rish987/trackswitch-manuform/things/usb_holder_cutout.stl

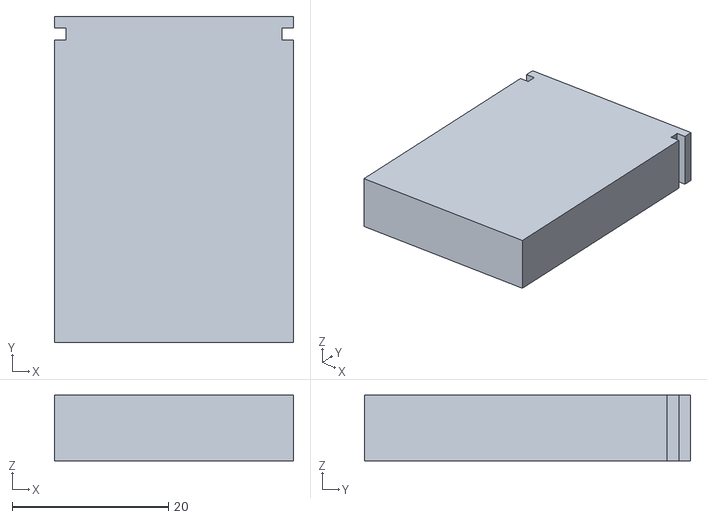
[picture p69: CAD file, 2021-12-29]
things/usb_holder_cutout.stl
30.6 x 41.7 x 8.40
