rish987/trackswitch-manuform/things/caps/matty3-deep-R5.stl

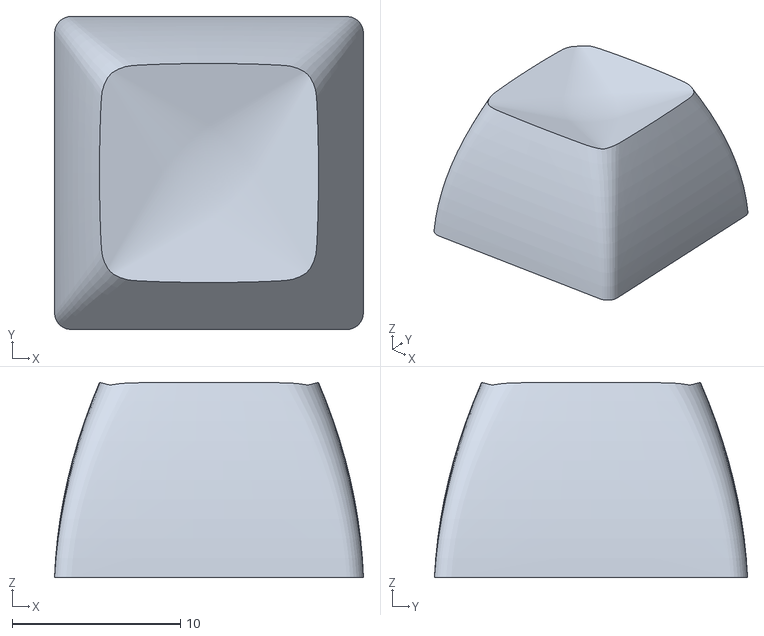
[picture p70: CAD file, 2022-04-26]
things/caps/matty3-deep-R5.stl
18.3 x 18.6 x 11.6
