rish987/trackswitch-manuform/things/usb_holder_w_reset_cutout.stl

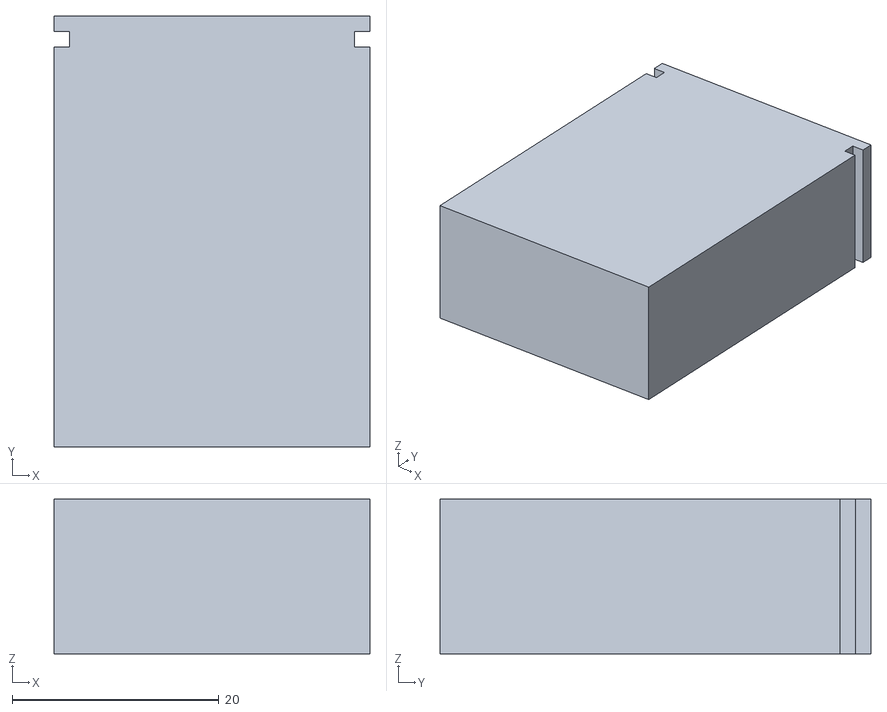
[picture p71: CAD file, 2021-12-29]
things/usb_holder_w_reset_cutout.stl
30.6 x 41.7 x 15.0
