rish987/trackswitch-manuform/things/caps/OEM-R2.stl

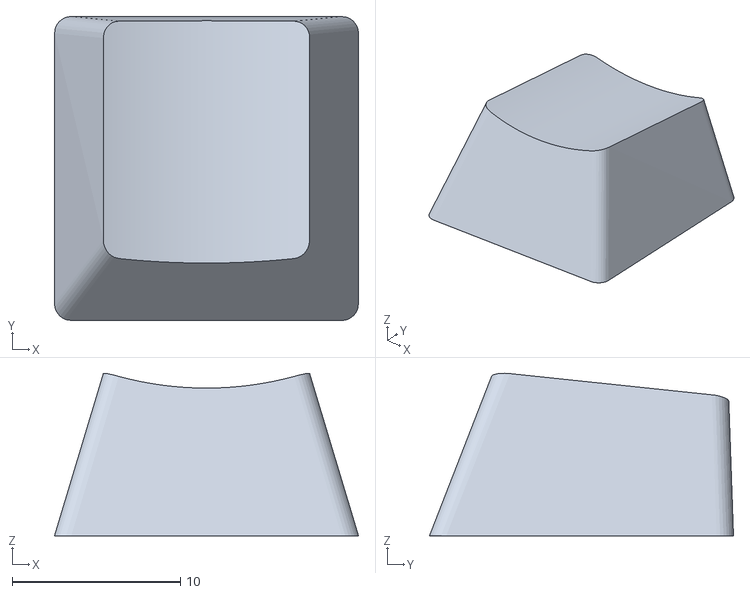
[picture p72: CAD file, 2022-04-26]
things/caps/OEM-R2.stl
18.0 x 18.0 x 9.65
