rish987/trackswitch-manuform/things/usb_holder_vertical.stl

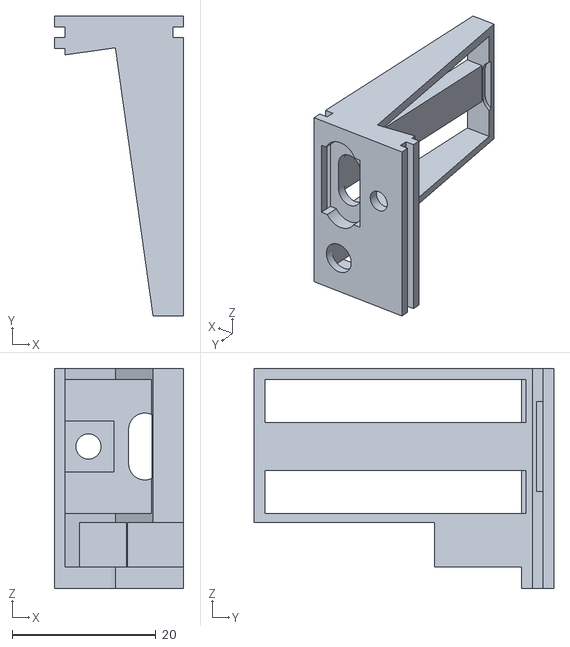
[picture p73: CAD file, 2021-12-29]
things/usb_holder_vertical.stl
18.0 x 41.7 x 30.6
