rish987/trackswitch-manuform/things/caps/matty3-deep-R3.stl

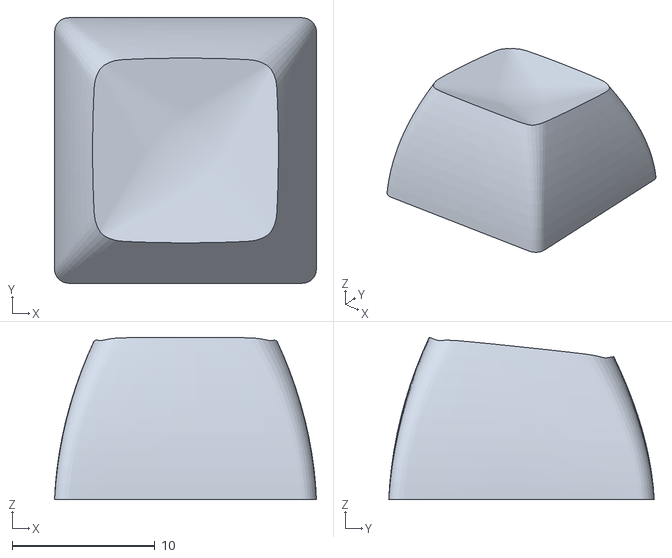
[picture p74: CAD file, 2022-04-26]
things/caps/matty3-deep-R3.stl
18.3 x 18.6 x 11.4
