rish987/trackswitch-manuform/things/usb_holder_w_reset.stl

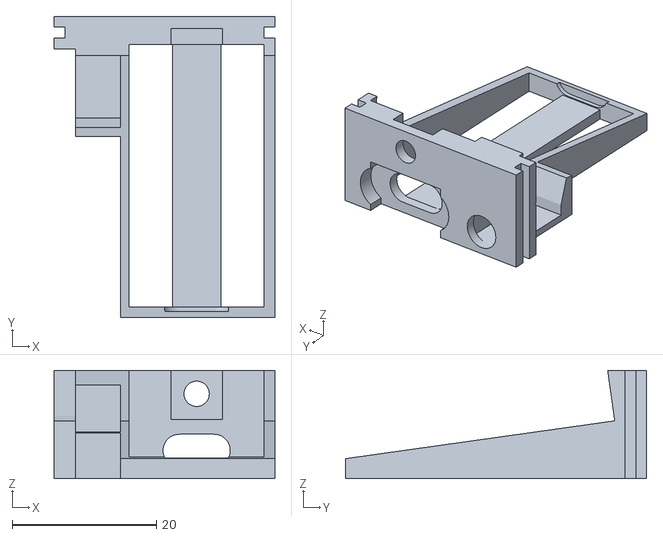
[picture p75: CAD file, 2021-12-29]
things/usb_holder_w_reset.stl
30.6 x 41.7 x 15.0
