rish987/trackswitch-manuform/things/wrist-rest-right.stl

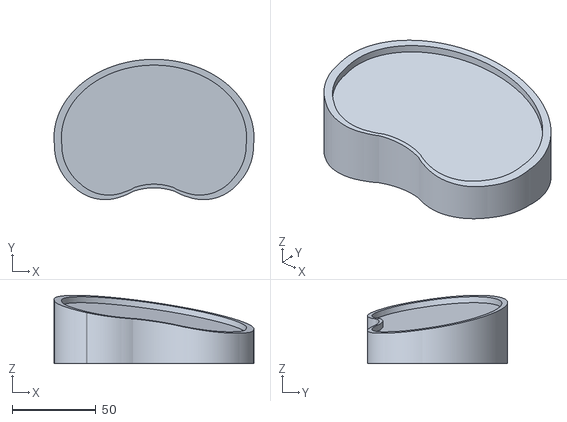
[picture p76: CAD file, 2021-08-13]
things/wrist-rest-right.stl
119.3 x 83.7 x 40.8
