rish987/trackswitch-manuform/things/caps/matty3-deep-R4.stl

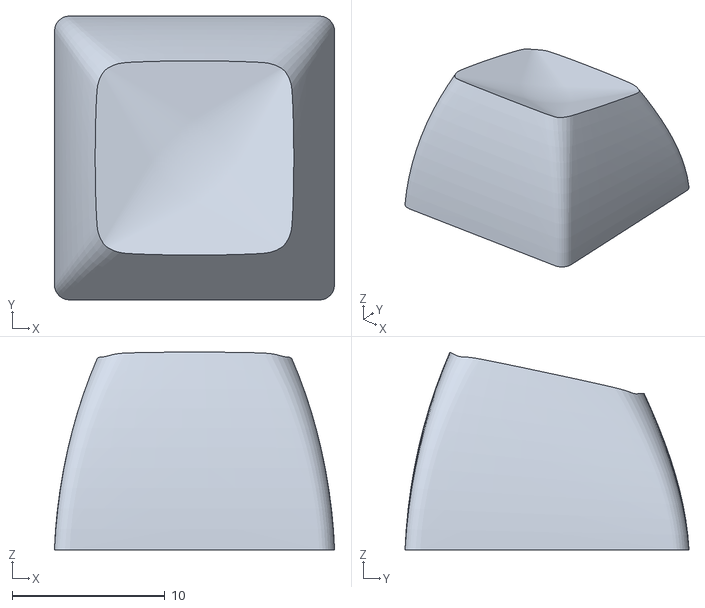
[picture p77: CAD file, 2022-04-26]
things/caps/matty3-deep-R4.stl
18.3 x 18.6 x 12.9
