rish987/trackswitch-manuform/things/okke_right.stl

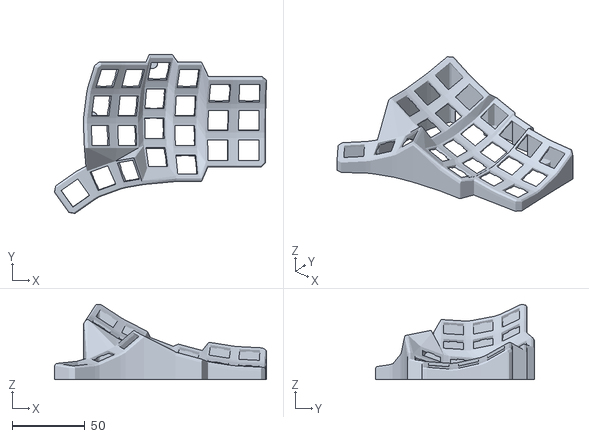
[picture p78: CAD file, 2020-12-27]
things/okke_right.stl
145.3 x 109.0 x 51.7
