rish987/trackswitch-manuform/things/caps/matty3-deep-R1.stl

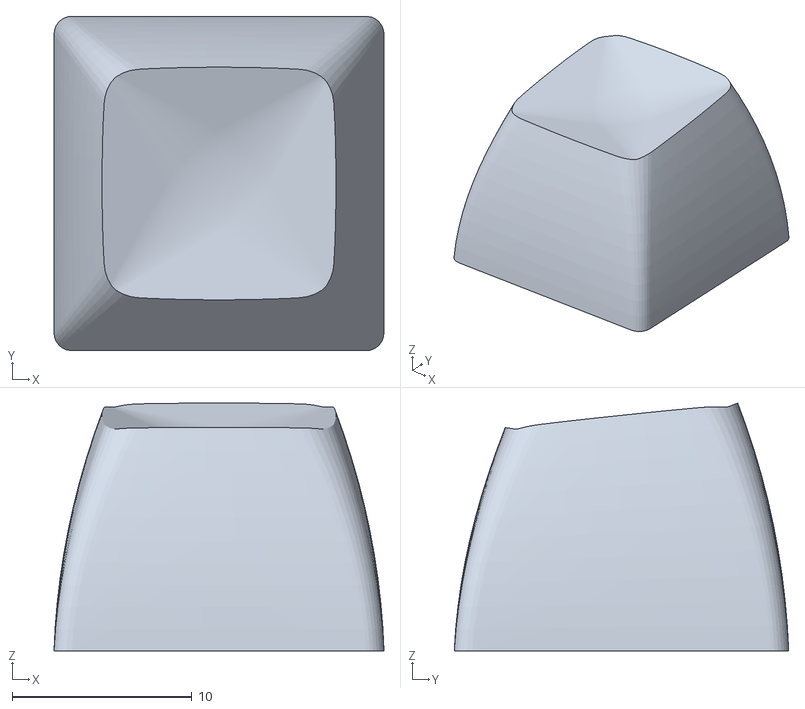
[picture p79: CAD file, 2022-04-26]
things/caps/matty3-deep-R1.stl
18.3 x 18.6 x 13.8
