rish987/trackswitch-manuform/things/caps/matty3-deep-R0.stl

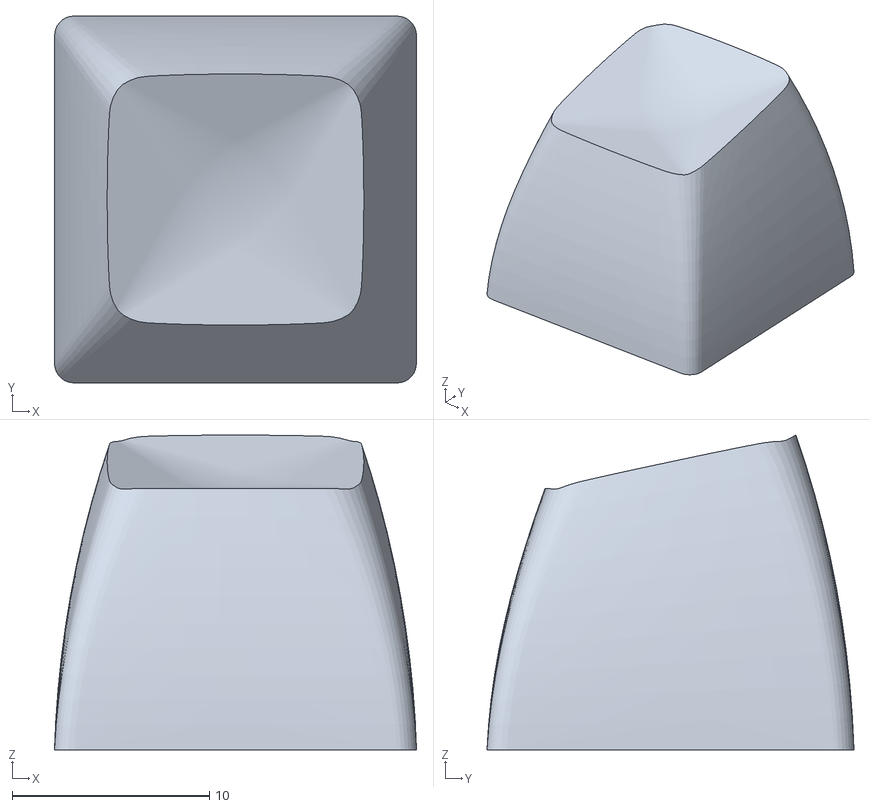
[picture p80: CAD file, 2022-04-26]
things/caps/matty3-deep-R0.stl
18.3 x 18.6 x 15.9
