rish987/trackswitch-manuform/things/caps/sa_row-5_length-1.stl

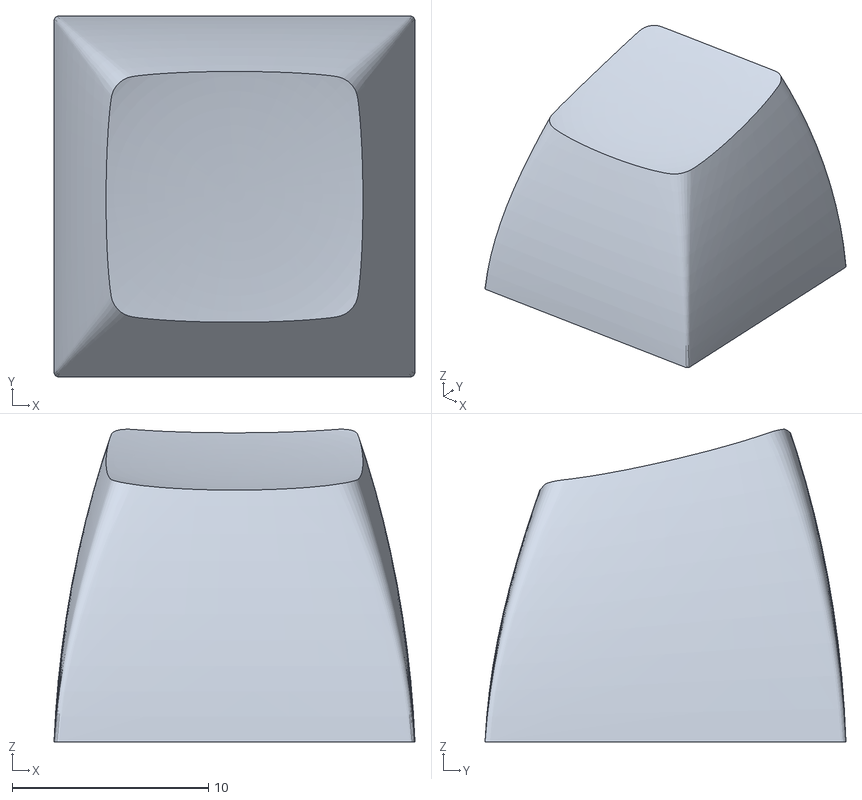
[picture p81: CAD file, 2022-02-21]
things/caps/sa_row-5_length-1.stl
18.4 x 18.4 x 15.9
