rish987/trackswitch-manuform/things/caps/SA-R1.stl

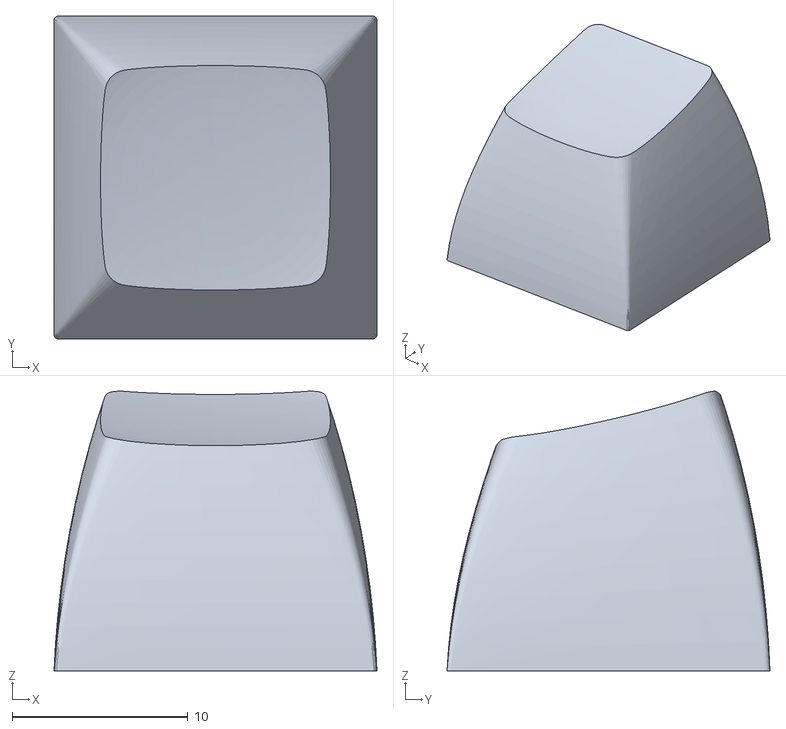
[picture p82: CAD file, 2022-02-21]
things/caps/SA-R1.stl
18.4 x 18.4 x 15.9
