rish987/trackswitch-manuform/things/caps/SA_R3_rounded.stl

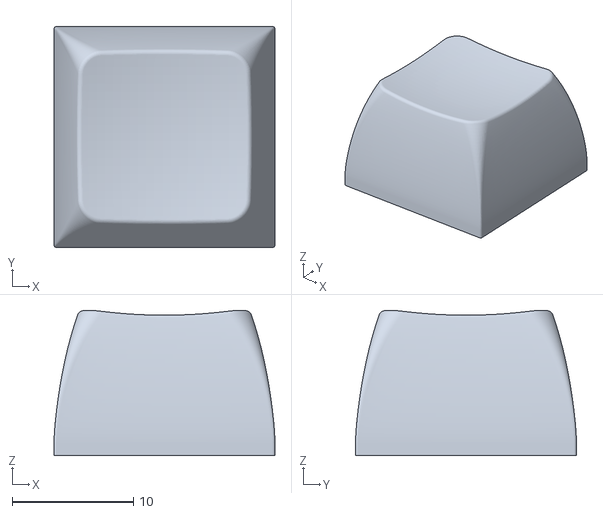
[picture p83: CAD file, 2022-02-21]
things/caps/SA_R3_rounded.stl
18.2 x 18.2 x 12.0
