rish987/trackswitch-manuform/things/caps/SA-R2.stl

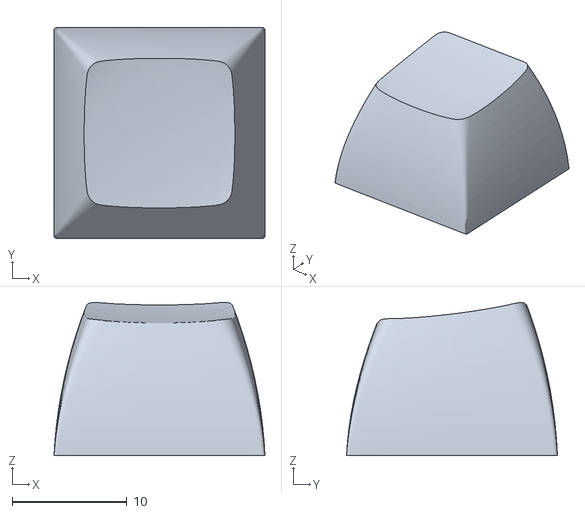
[picture p84: CAD file, 2022-02-21]
things/caps/SA-R2.stl
18.4 x 18.4 x 13.4
