rish987/trackswitch-manuform/things/caps/SA-R0.stl

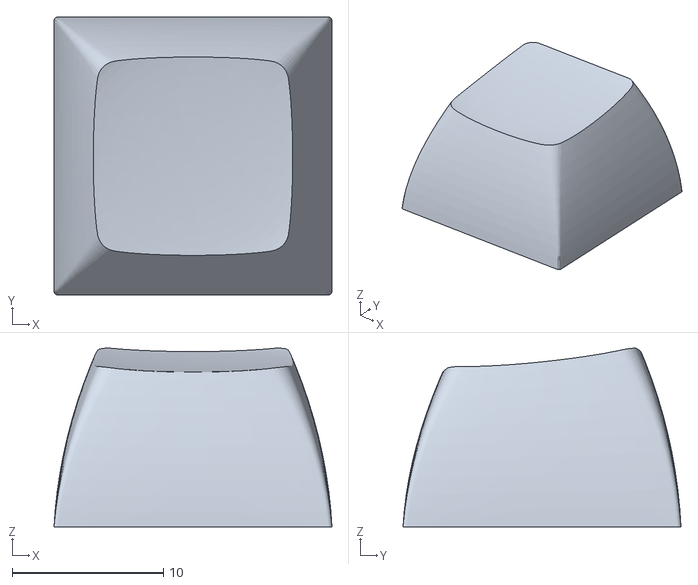
[picture p85: CAD file, 2022-02-21]
things/caps/SA-R0.stl
18.4 x 18.4 x 11.8
