rish987/trackswitch-manuform/things/caps/SA-R3C_16.stl

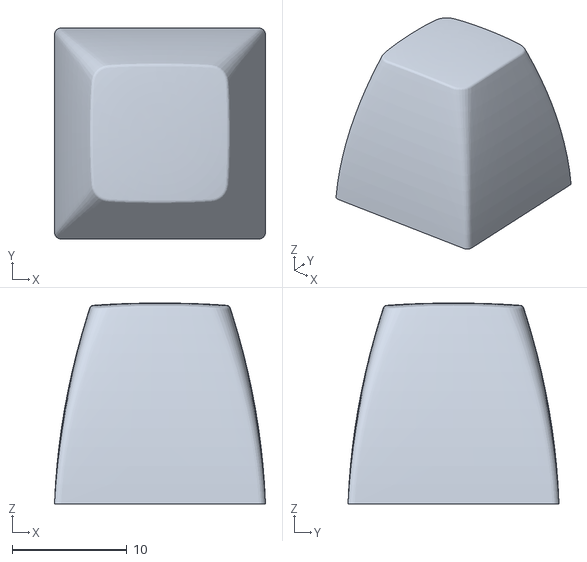
[picture p86: CAD file, 2021-08-07]
things/caps/SA-R3C_16.stl
18.4 x 18.4 x 17.5
